WH-Wei/Cross-Flow-Fan-ITX-DIY/solidworks版本图纸/显卡防尘网.SLDPRT

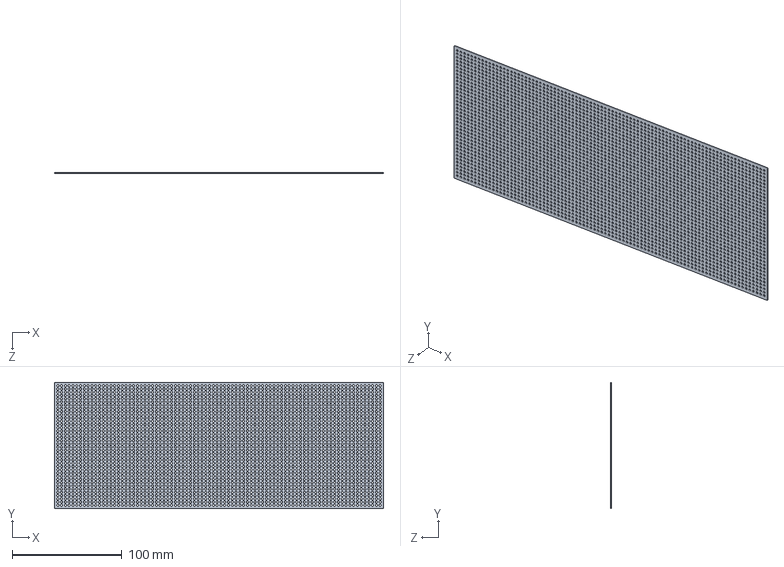
[picture p21: CAD file, 2023-03-17]
solidworks版本图纸/显卡防尘网.SLDPRT
300.0 x 115.0 x 1.00 mm
