WH-Wei/Cross-Flow-Fan-ITX-DIY/solidworks版本图纸/铜柱_发黑_3x6+6.SLDPRT

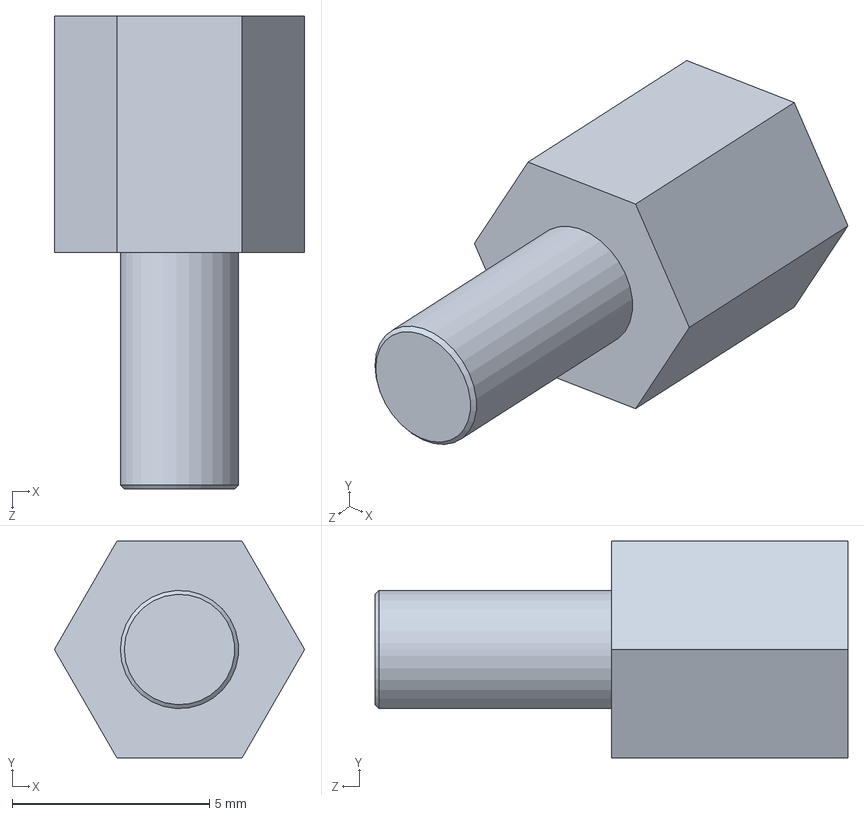
[picture p22: CAD file, 2023-03-17]
solidworks版本图纸/铜柱_发黑_3x6+6.SLDPRT
6.35 x 5.50 x 12.0 mm
