WH-Wei/Cross-Flow-Fan-ITX-DIY/solidworks版本图纸/M3_D6_10.SLDPRT

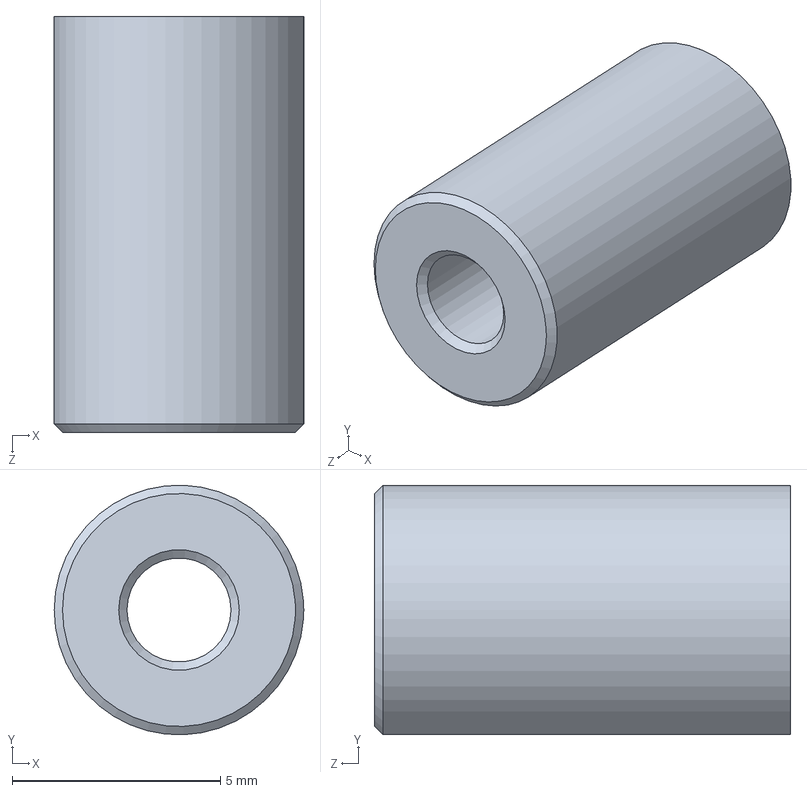
[picture p23: CAD file, 2023-03-17]
solidworks版本图纸/M3_D6_10.SLDPRT
6.00 x 6.00 x 10.0 mm
