WH-Wei/Cross-Flow-Fan-ITX-DIY/solidworks版本图纸/重启键.SLDPRT

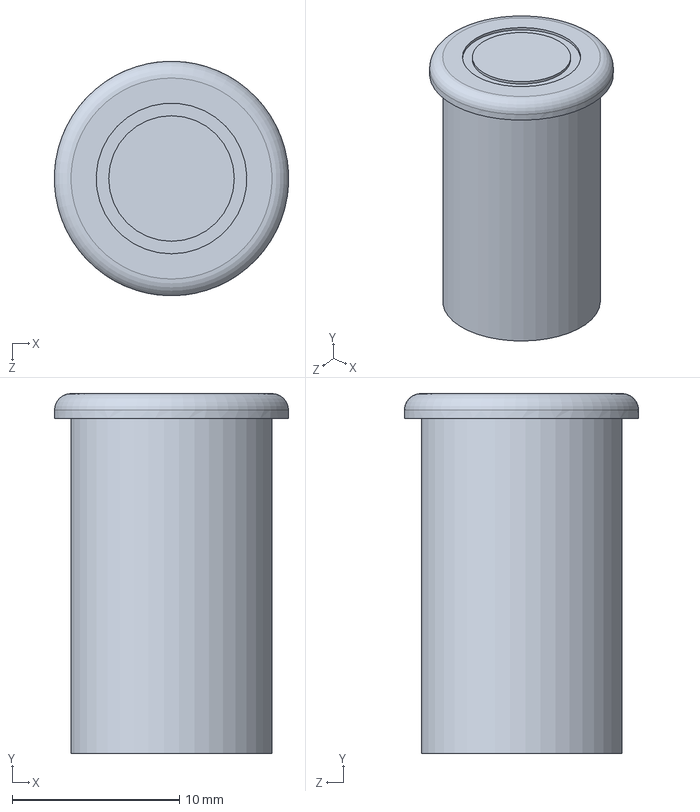
[picture p24: CAD file, 2023-03-17]
solidworks版本图纸/重启键.SLDPRT
14.0 x 21.5 x 14.0 mm
