WH-Wei/Cross-Flow-Fan-ITX-DIY/solidworks版本图纸/机箱侧板.SLDPRT

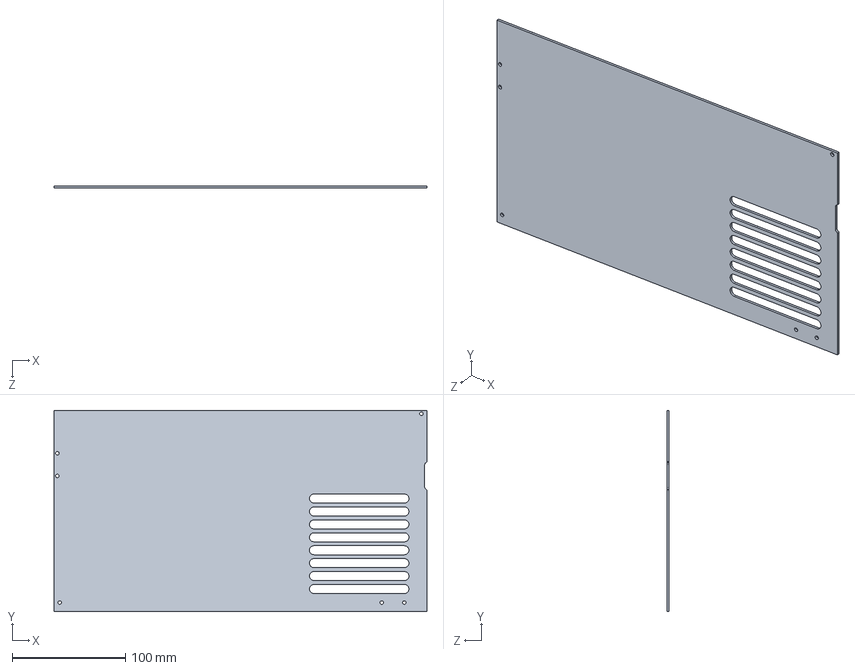
[picture p25: CAD file, 2023-03-17]
solidworks版本图纸/机箱侧板.SLDPRT
330.0 x 178.0 x 2.00 mm
