WH-Wei/Cross-Flow-Fan-ITX-DIY/solidworks版本图纸/7mmG4宝塔头.SLDPRT

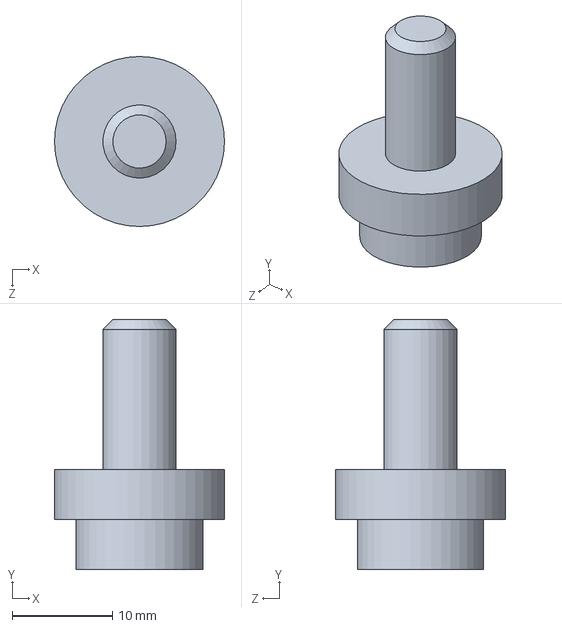
[picture p26: CAD file, 2023-03-17]
solidworks版本图纸/7mmG4宝塔头.SLDPRT
17.0 x 25.0 x 17.0 mm
