WH-Wei/Cross-Flow-Fan-ITX-DIY/solidworks版本图纸/ROG_STRIX_Z690I.SLDPRT

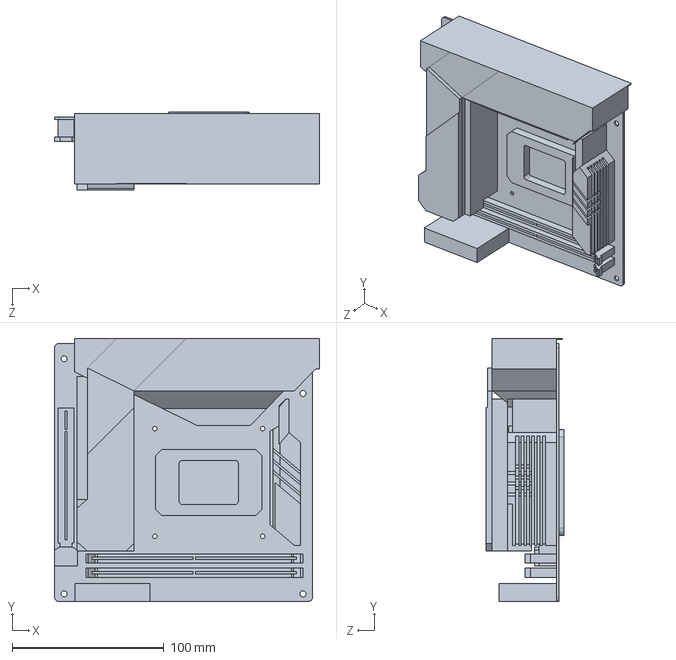
[picture p27: CAD file, 2023-03-17]
solidworks版本图纸/ROG_STRIX_Z690I.SLDPRT
174.7 x 173.4 x 51.2 mm
