WH-Wei/Cross-Flow-Fan-ITX-DIY/solidworks版本图纸/Alphacool280HPE-30.SLDPRT

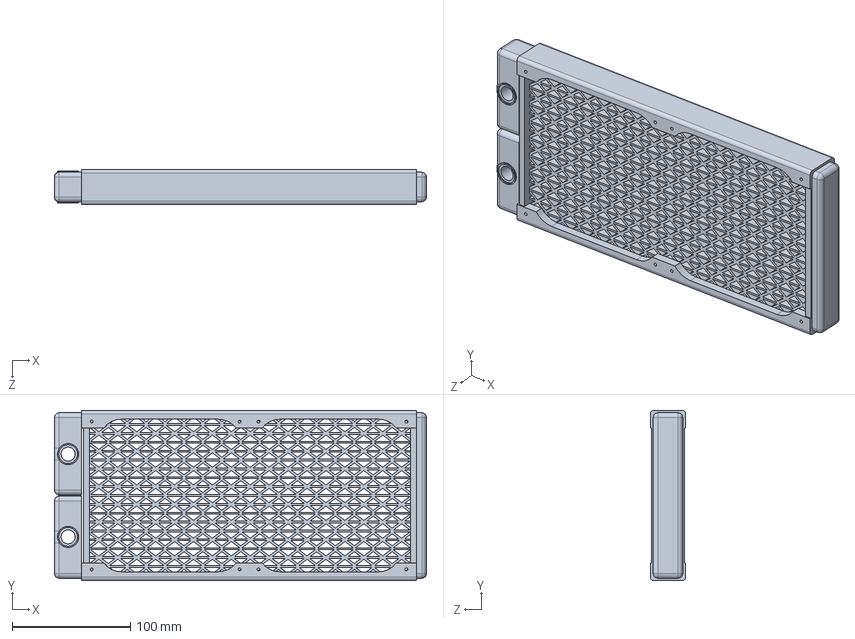
[picture p28: CAD file, 2023-03-17]
solidworks版本图纸/Alphacool280HPE-30.SLDPRT
314.5 x 144.0 x 30.0 mm
