WH-Wei/Cross-Flow-Fan-ITX-DIY/solidworks版本图纸/PA_43250DC12.SLDPRT

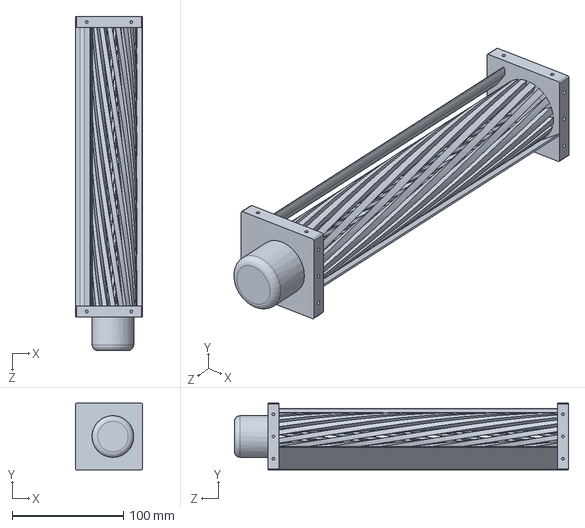
[picture p29: CAD file, 2023-03-17]
solidworks版本图纸/PA_43250DC12.SLDPRT
60.0 x 60.0 x 300.0 mm
