WH-Wei/Cross-Flow-Fan-ITX-DIY/solidworks版本图纸/机箱风道前隔板.SLDPRT

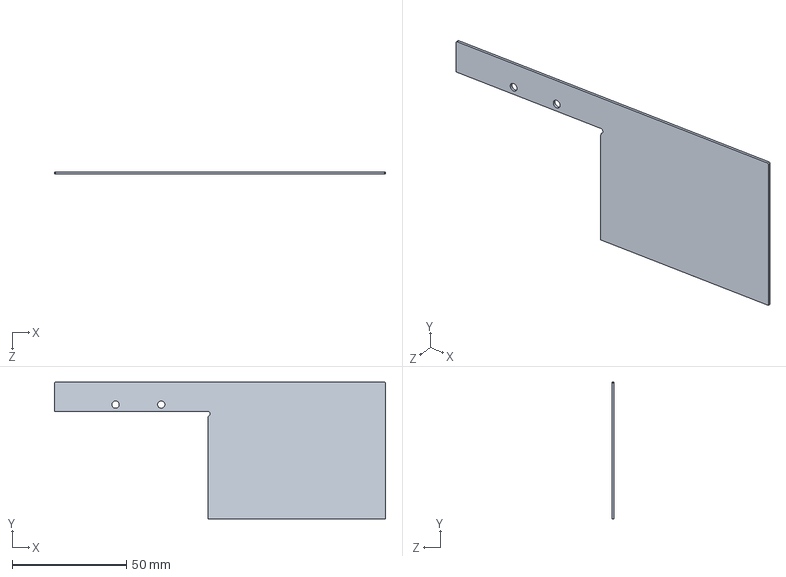
[picture p30: CAD file, 2023-03-17]
solidworks版本图纸/机箱风道前隔板.SLDPRT
145.0 x 60.0 x 1.00 mm
