WH-Wei/Cross-Flow-Fan-ITX-DIY/solidworks版本图纸/USB3Gen2x2.SLDPRT

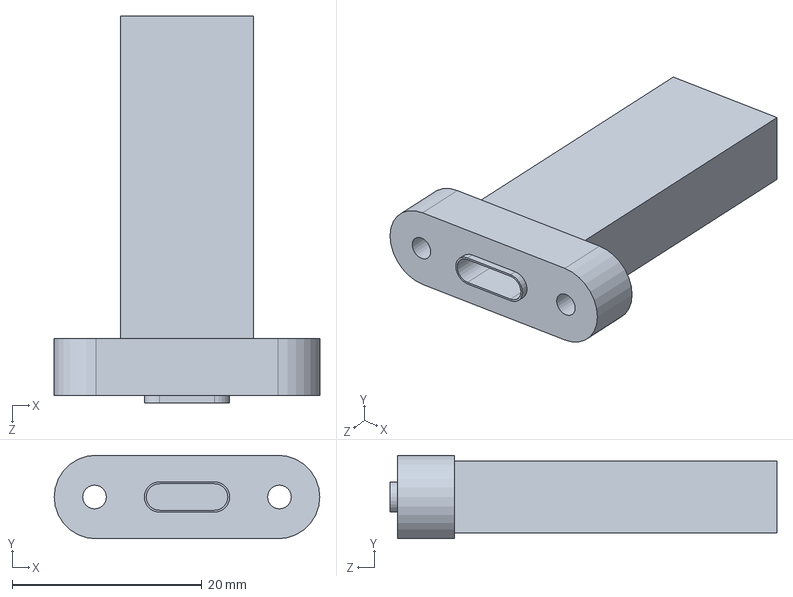
[picture p31: CAD file, 2023-03-17]
solidworks版本图纸/USB3Gen2x2.SLDPRT
28.0 x 8.80 x 40.8 mm
