WH-Wei/Cross-Flow-Fan-ITX-DIY/solidworks版本图纸/10_10_6铝方M3.SLDPRT

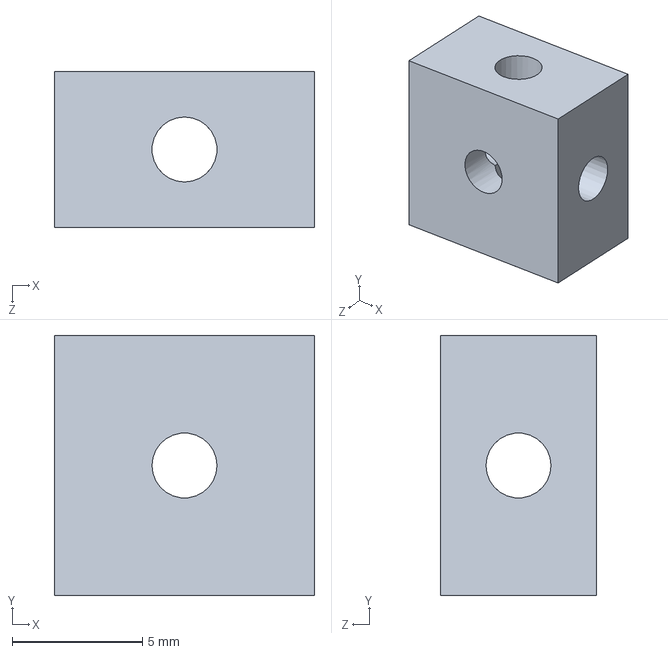
[picture p32: CAD file, 2023-03-17]
solidworks版本图纸/10_10_6铝方M3.SLDPRT
10.0 x 10.0 x 6.00 mm
