WH-Wei/Cross-Flow-Fan-ITX-DIY/solidworks版本图纸/电源插座.SLDPRT

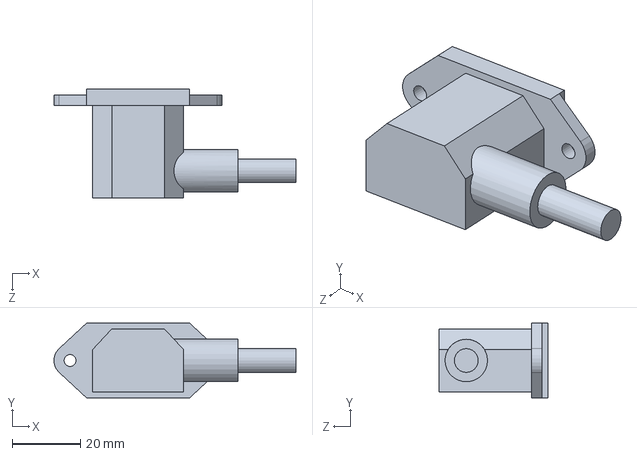
[picture p33: CAD file, 2023-03-17]
solidworks版本图纸/电源插座.SLDPRT
71.1 x 22.0 x 32.0 mm
