WH-Wei/Cross-Flow-Fan-ITX-DIY/solidworks版本图纸/CoolerMaster_sfx_V850.SLDPRT

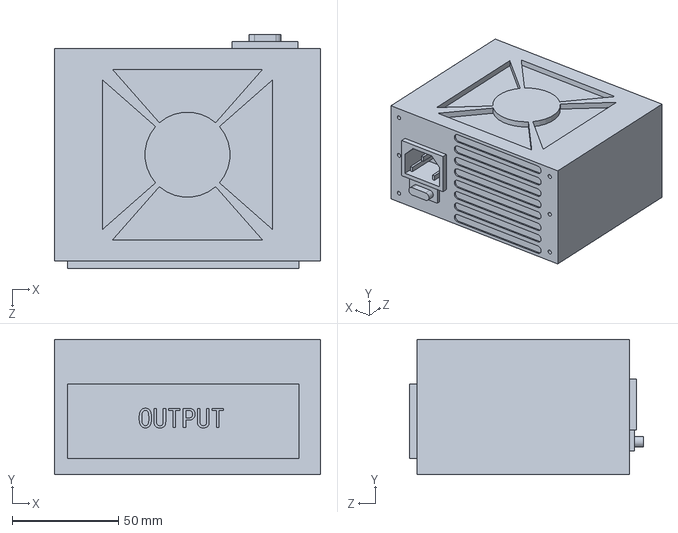
[picture p34: CAD file, 2023-03-17]
solidworks版本图纸/CoolerMaster_sfx_V850.SLDPRT
125.0 x 63.5 x 110.0 mm
