WH-Wei/Cross-Flow-Fan-ITX-DIY/solidworks版本图纸/30mm风扇.SLDPRT

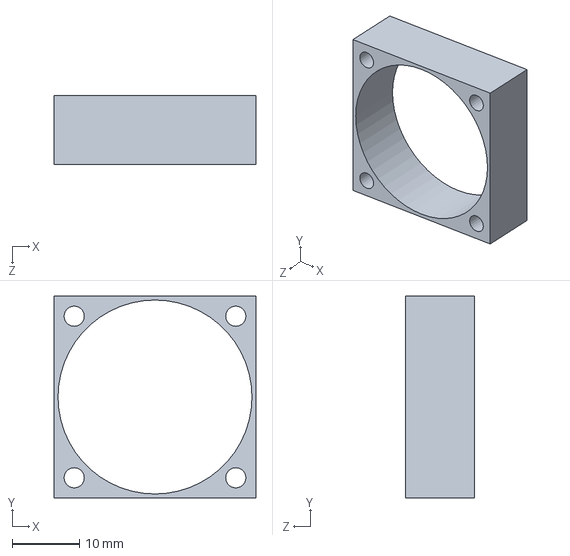
[picture p35: CAD file, 2023-03-17]
solidworks版本图纸/30mm风扇.SLDPRT
30.0 x 30.0 x 10.3 mm
