WH-Wei/Cross-Flow-Fan-ITX-DIY/solidworks版本图纸/前面板.SLDPRT

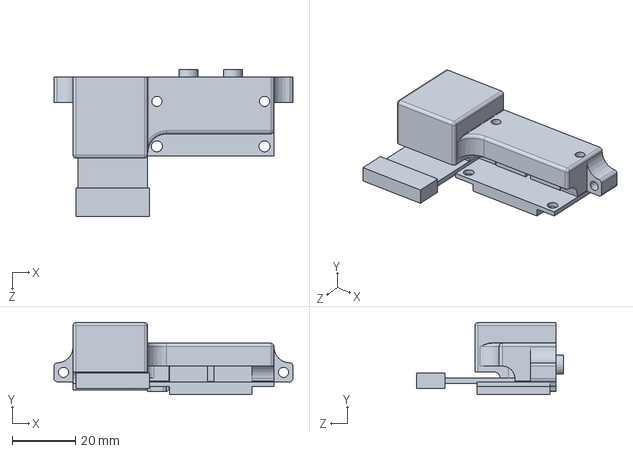
[picture p36: CAD file, 2023-03-17]
solidworks版本图纸/前面板.SLDPRT
75.5 x 22.8 x 46.3 mm
